Magnum-Monk/KeebIsSplit/3D/STP/CASE_LEFT_BOT_CLIPS.STP

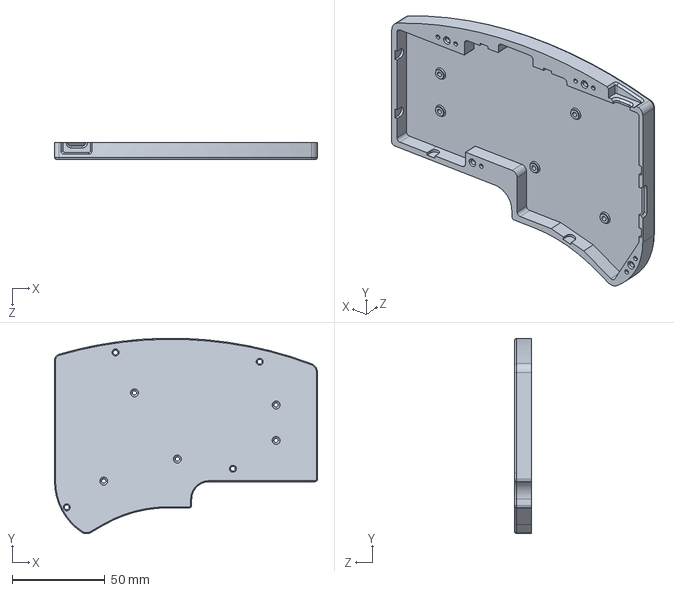
[picture p17: CAD file, 2025-03-03]
3D/STP/CASE_LEFT_BOT_CLIPS.STP
141.5 x 105.1 x 9.05 mm
