Magnum-Monk/KeebIsSplit/3D/ATMEGA32U4_TYPE_C.SLDPRT

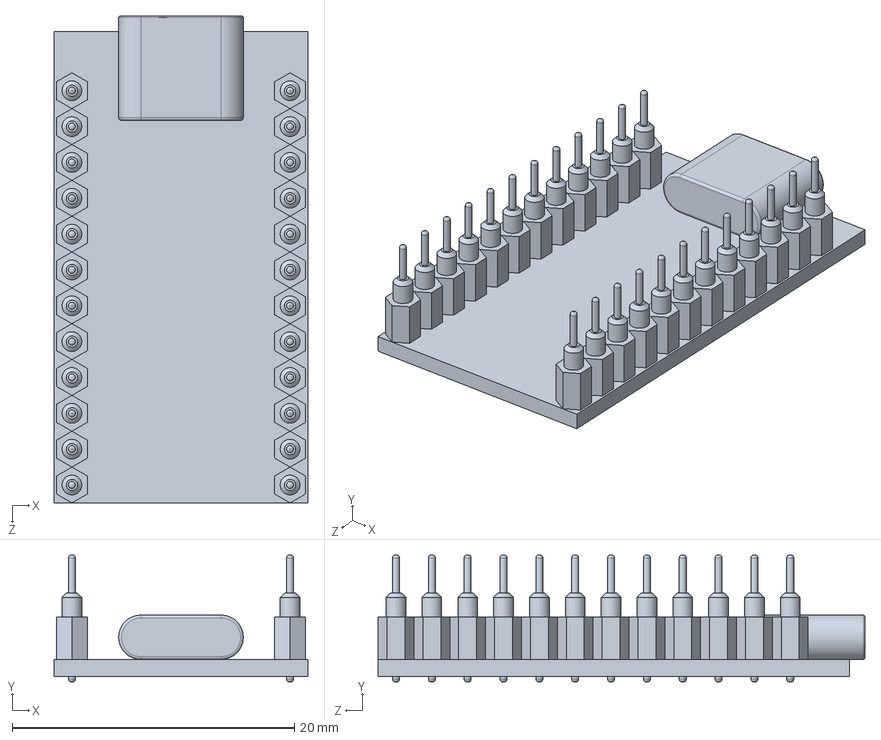
[picture p18: CAD file, 2025-03-03]
3D/ATMEGA32U4_TYPE_C.SLDPRT
18.0 x 9.00 x 34.5 mm
