Magnum-Monk/KeebIsSplit/3D/MX/针脚.SLDPRT

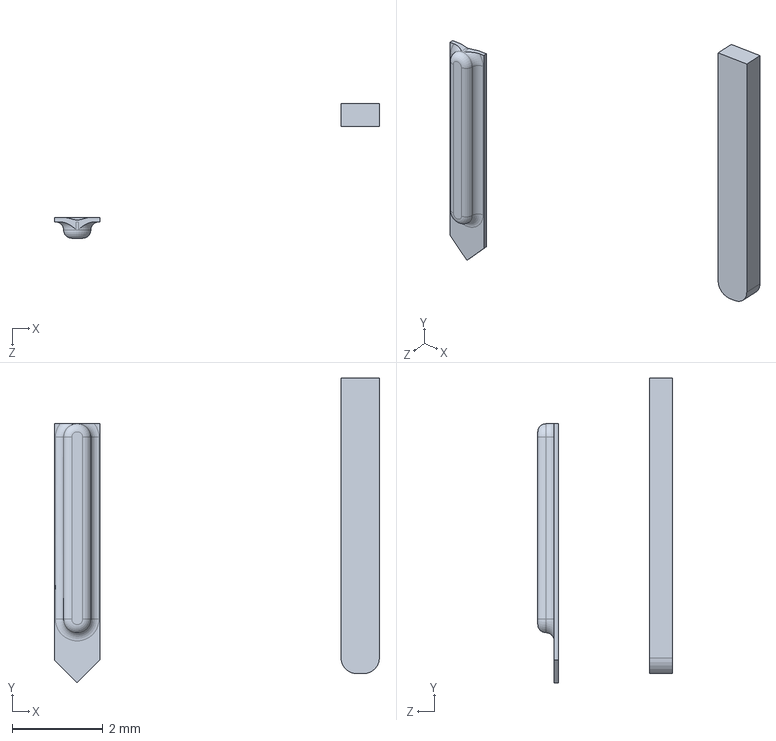
[picture p19: CAD file, 2025-03-04]
3D/MX/针脚.SLDPRT
7.15 x 6.70 x 2.96 mm
