Magnum-Monk/KeebIsSplit/3D/MX/MX轴 轴体 底部.SLDPRT

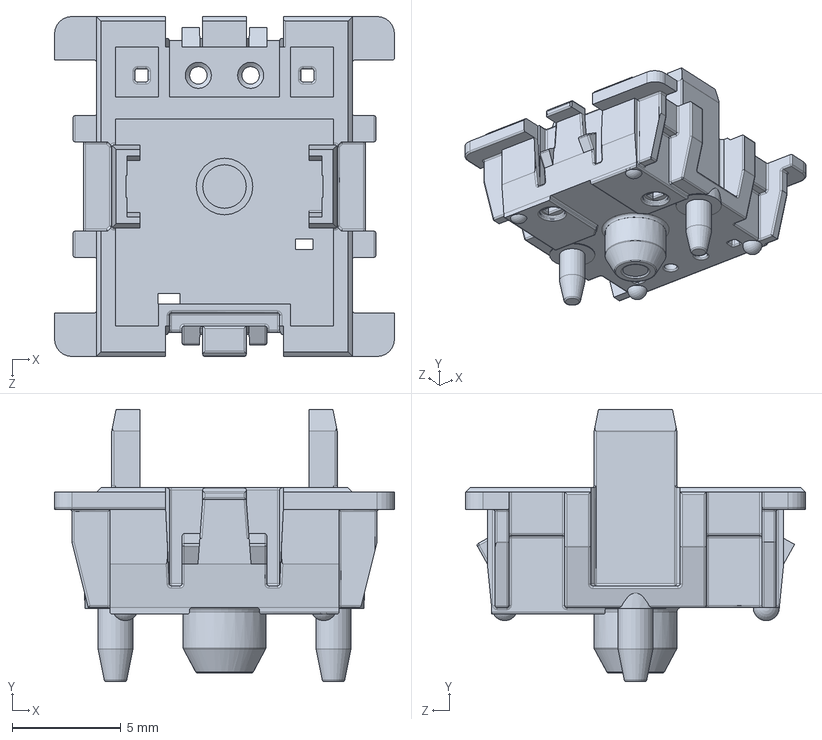
[picture p20: CAD file, 2025-03-04]
3D/MX/MX轴 轴体 底部.SLDPRT
15.6 x 12.5 x 15.6 mm
