Magnum-Monk/KeebIsSplit/3D/MX/r3_100.SLDPRT

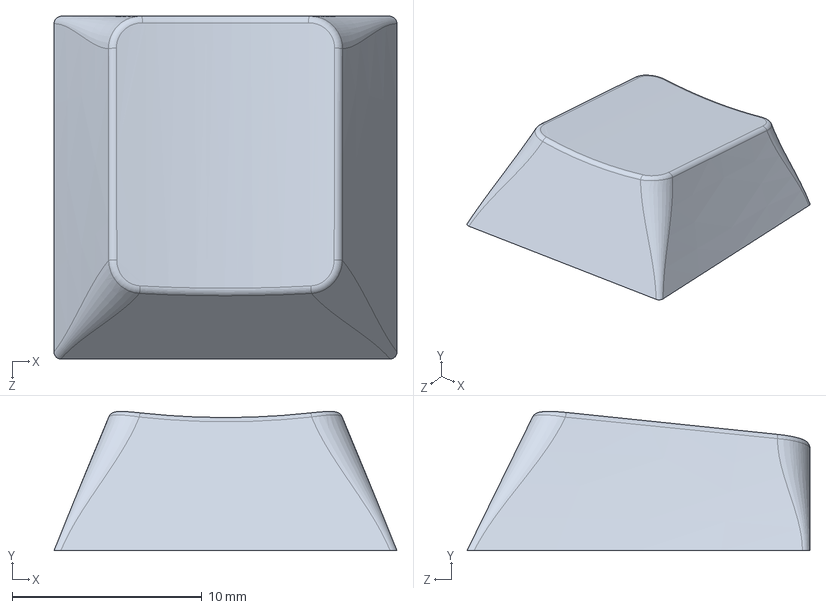
[picture p21: CAD file, 2025-03-04]
3D/MX/r3_100.SLDPRT
18.1 x 7.35 x 18.1 mm
